mirage335/NetPLC/productionStatic/hacdcCNC/NetPLC/outp5_masked.png

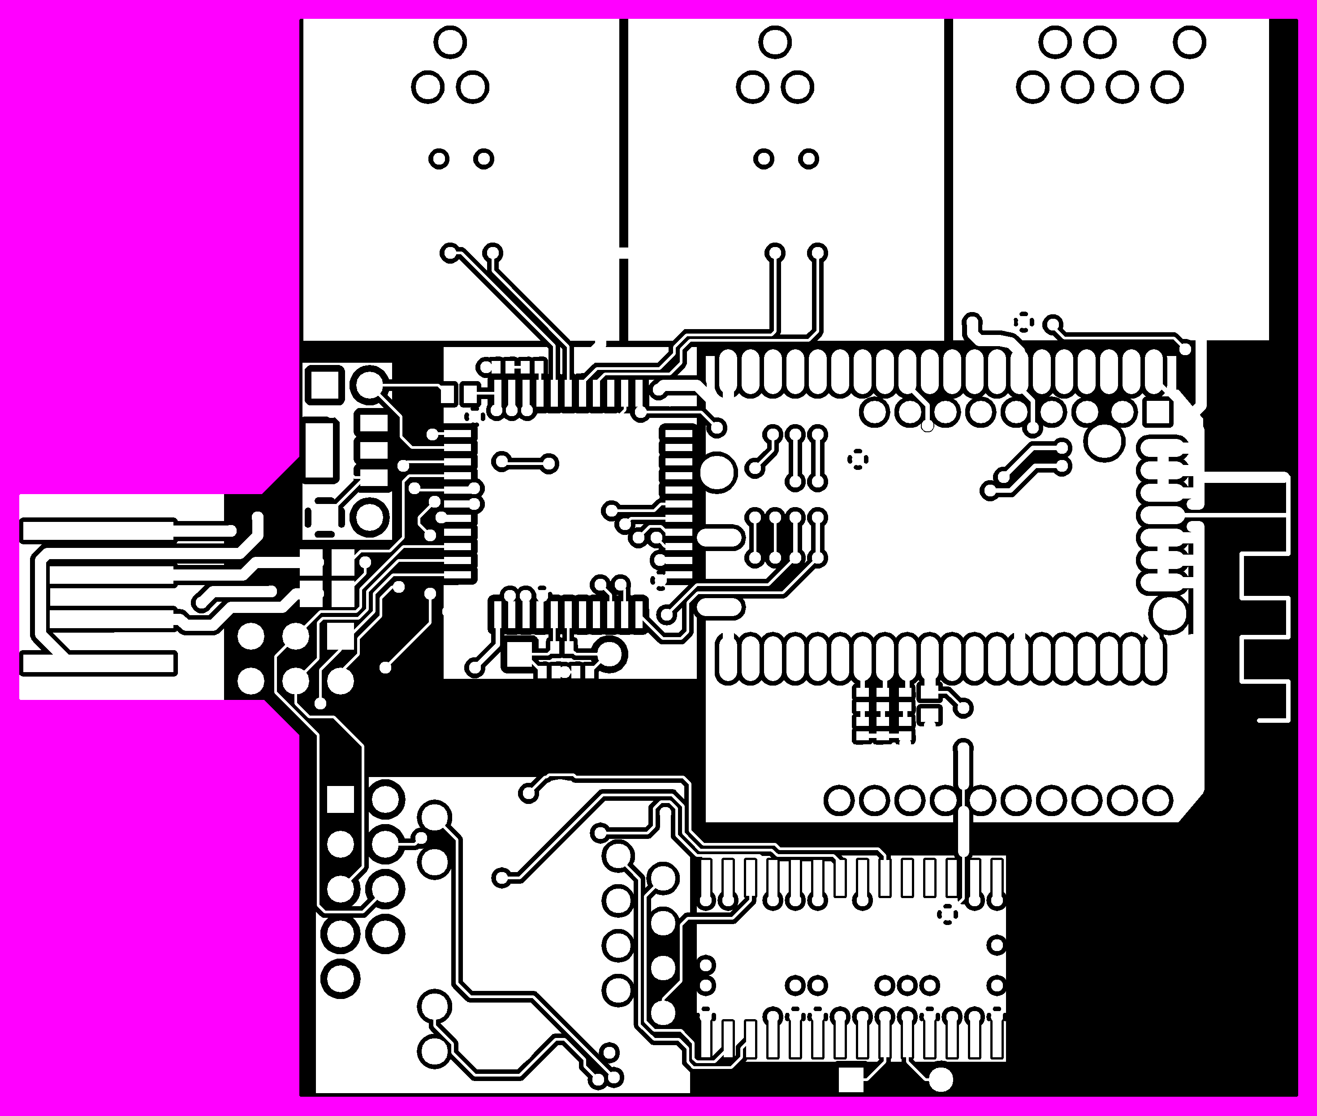
productionStatic/hacdcCNC/NetPLC/outp5_masked.png
