mirage335/NetPLC/productionStatic/hacdcCNC/NetPLC/outp6_traced.png

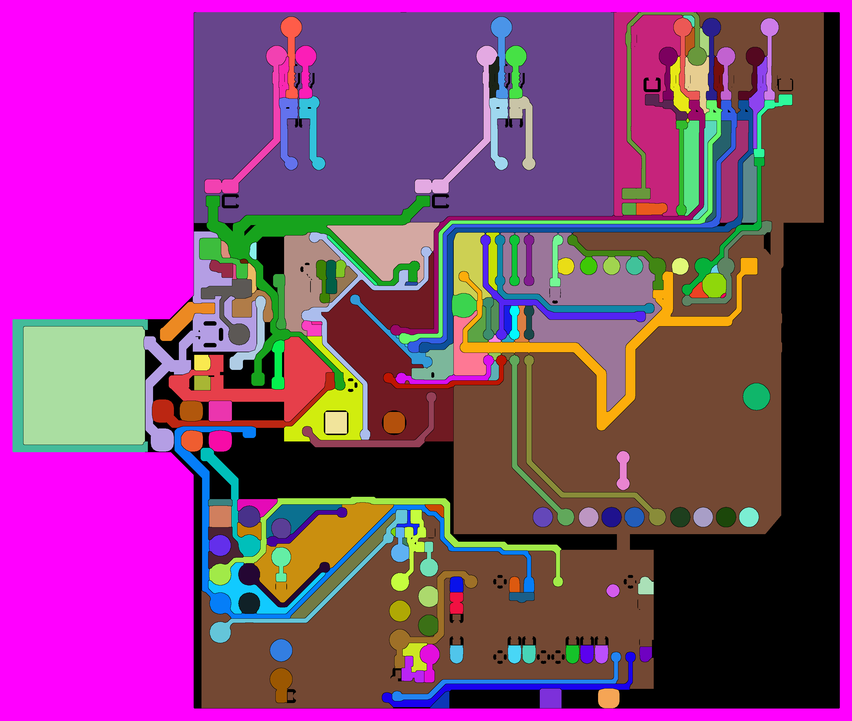
productionStatic/hacdcCNC/NetPLC/outp6_traced.png
