mirage335/NetPLC/productionStatic/hacdcCNC/NetPLC/outp7_traced.png

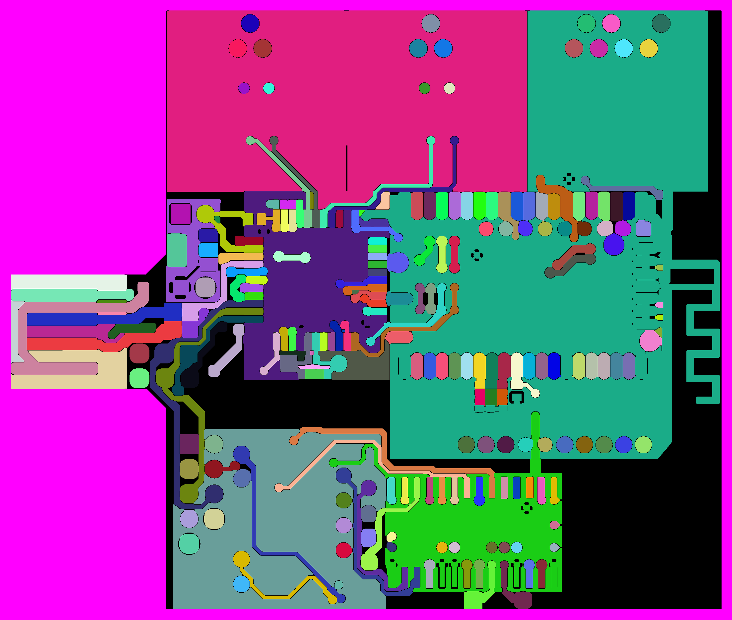
productionStatic/hacdcCNC/NetPLC/outp7_traced.png
