mirage335/NetPLC/productionStatic/hacdcCNC/NetPLC/outp8_traced.png

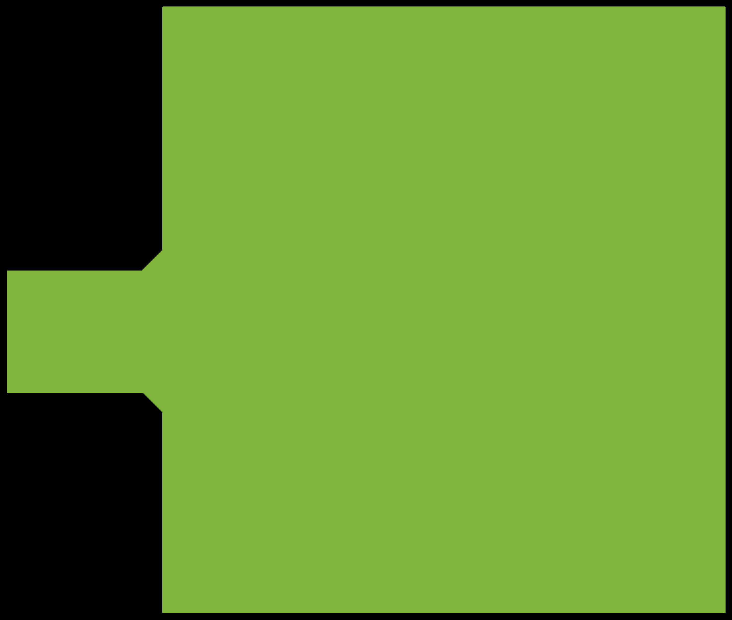
productionStatic/hacdcCNC/NetPLC/outp8_traced.png
